onsar/osec/images/pcb_alimentacion.jpeg

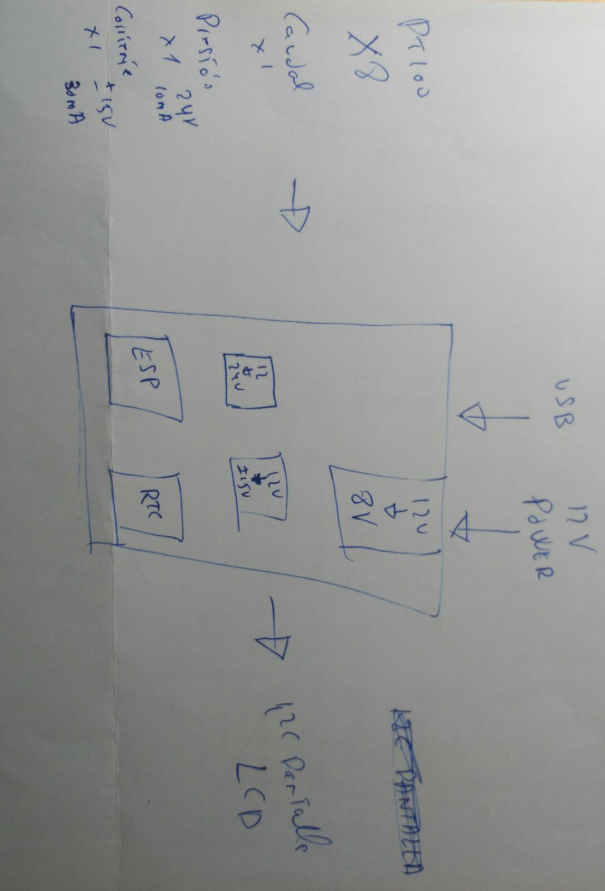
images/pcb_alimentacion.jpeg
