onsar/osec/images/analogic_circuit_test.png

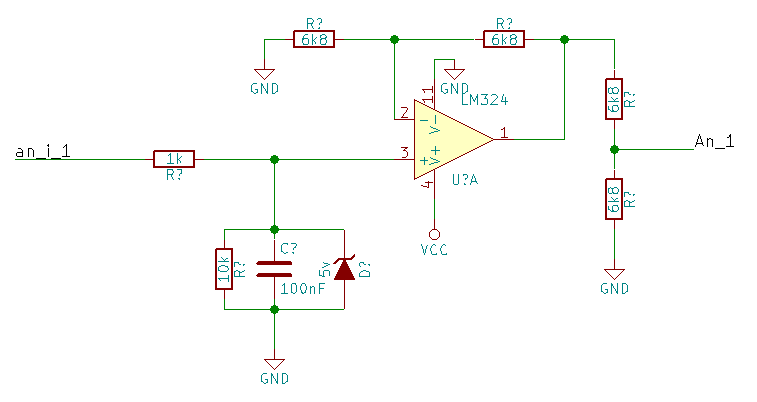
images/analogic_circuit_test.png
