onsar/osec/arduino/EmonESP/src/src.ino

/*
 * -------------------------------------------------------------------
 * EmonESP Serial to Emoncms gateway
 * -------------------------------------------------------------------
 * Adaptation of Chris Howells OpenEVSE ESP Wifi
 * by Trystan Lea, Glyn Hudson, OpenEnergyMonitor
 * All adaptation GNU General Public License as below.
 *
 * -------------------------------------------------------------------
 *
 * This file is part of OpenEnergyMonitor.org project.
 * EmonESP is free software; you can redistribute it and/or modify
 * it under the terms of the GNU General Public License as published by
 * the Free Software Foundation; either version 3, or (at your option)
 * any later version.
 * EmonESP is distributed in the hope that it will be useful,
 * but WITHOUT ANY WARRANTY; without even the implied warranty of
 * MERCHANTABILITY or FITNESS FOR A PARTICULAR PURPOSE.  See the
 * GNU General Public License for more details.
 * You should have received a copy of the GNU General Public License
 * along with EmonESP; see the file COPYING.  If not, write to the
 * Free Software Foundation, Inc., 59 Temple Place - Suite 330,
 * Boston, MA 02111-1307, USA.
 */

#include "emonesp.h"
#include "config.h"
#include "wifi.h"
#include "web_server.h"
#include "ota.h"
#include "input.h"
#include "emoncms.h"
#include "mqtt.h"

// -------------------------------------------------------------------
// SETUP
// -------------------------------------------------------------------
void setup() {
  delay(2000);

  Serial.begin(115200);
#ifdef DEBUG_SERIAL1
  Serial1.begin(115200);
#endif

  DEBUG.println();
  DEBUG.print("EmonESP ");
  DEBUG.println(ESP.getChipId());
  DEBUG.println("Firmware: "+ currentfirmware);

  // Read saved settings from the config
  config_load_settings();

  // Initialise the WiFi
  wifi_setup();

  // Bring up the web server
  web_server_setup();

  // Start the OTA update systems
  ota_setup();

  DEBUG.println("Server started");

  delay(100);
} // end setup

// -------------------------------------------------------------------
// LOOP
// -------------------------------------------------------------------
void loop()
{
  ota_loop();
  web_server_loop();
  wifi_loop();

  // delay(10000);
  String input = "";
  // input = "ct1:3935,ct2:325,t1:12.5,t2:16.9,t3:11.2,t4:34.7";
  boolean gotInput = input_get(input);

  if (wifi_mode == WIFI_MODE_STA || wifi_mode == WIFI_MODE_AP_AND_STA)
  {
    if(emoncms_apikey != 0 && gotInput) {
      emoncms_publish(input);
    }
    if(mqtt_server != 0)
    {
      mqtt_loop();
      if(gotInput) {
        mqtt_publish(input);
      }
    }
  }
} // end loop
