onsar/osec/arduino/water_flow_test/flow_sensor_configuration.h

#ifndef flow_sensor_configuration_h
#define flow_sensor_configuration_h


#define FLOW_DEVICES_NUMBER 2

#define  FLOW_INPUT_1  2
#define  FLOW_SENSOR_NAME_1 " ENTRADA DE AGUA" 

#define  FLOW_INPUT_2  3
#define  FLOW_SENSOR_NAME_2 " AGUA CALIENTE" 

#endif
