onsar/osec/pruebas_nodemcu/prueba_18b20/prueba_18b20.ino

// ESP8266 DS18B20 ArduinoIDE Thingspeak IoT Example code
// http://vaasa.hacklab.fi
//
// https://github.com/milesburton/Arduino-Temperature-Control-Library
// https://gist.github.com/jeje/57091acf138a92c4176a


#include <OneWire.h>
#include <ESP8266WiFi.h>
#include <ESP8266WebServer.h>
#include <DallasTemperature.h>

#define ONE_WIRE_BUS D2


const char* host = "api.thingspeak.com"; // Your domain  
String ApiKey = "FR5DZBZG42NI9E7T";
String path = "/update?key=" + ApiKey + "&field1=";  


OneWire oneWire(ONE_WIRE_BUS);
DallasTemperature DS18B20(&oneWire);

const char* ssid = "casaelobrero";
const char* pass = "lacosamasbonitadelmundo";


char temperatureString[6];

uint8_t numberOfDevices=0;

void setup(void){
  Serial.begin(115200);
  Serial.println("");
  
  WiFi.begin(ssid, pass);
  // Wait for connection
  while (WiFi.status() != WL_CONNECTED) {
    delay(100);
    Serial.print(".");
  }
  
  Serial.println("");
  Serial.print("Connected to ");
  Serial.println(ssid);
  Serial.print("IP address: ");
  Serial.println(WiFi.localIP());

  DS18B20.begin();
  delay(1000);
   

}

float getTemperature() {
  Serial.println ("inicio funcion getTemperature()");
  float temp;
  do {
   Serial.println ("do"); 
    


    numberOfDevices = DS18B20.getDeviceCount();
    delay(1000);
    Serial.print(F("numberOfDevices = "));
    Serial.println(numberOfDevices);

    DS18B20.requestTemperatures(); 

    delay(1000);
 
    temp = DS18B20.getTempCByIndex(0);

    delay(1000);
    
    Serial.println ("CBy"); 
    Serial.println (temp); 
    delay(100);
  } while (temp == 85.0 || temp == (-127.0));
  return temp;
}


void loop() {
  Serial.println ("inicio bucle");
  float temperature = getTemperature();
  
  Serial.println ("final getTemperature()");
  
  dtostrf(temperature, 2, 2, temperatureString);

  Serial.println ("final dtostrf()");
  
  // send temperature to the serial console
  Serial.println(temperatureString);

  WiFiClient client;
  const int httpPort = 80;
  if (!client.connect(host, httpPort)) {
    Serial.println("connection failed");
    return;
  }

  client.print(String("GET ") + path + temperatureString + " HTTP/1.1\r\n" +
               "Host: " + host + "\r\n" + 
               "Connection: keep-alive\r\n\r\n");
  delay(500);
  Serial.println ("final bucle");

}
